C19HOP/WiSafe2-to-HomeAssistant-Bridge/HA/getting-id-from-new-device.png

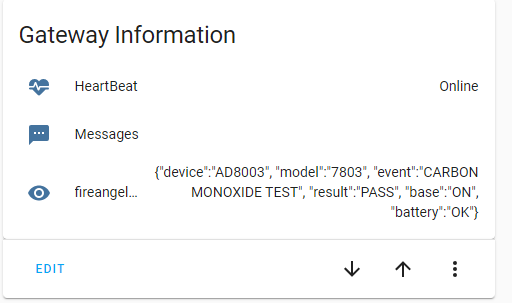
HA/getting-id-from-new-device.png
