C19HOP/WiSafe2-to-HomeAssistant-Bridge/HA/network-paired.png

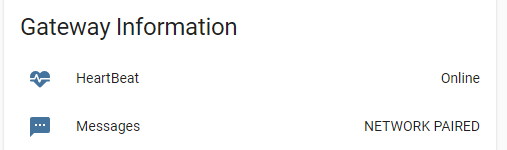
HA/network-paired.png
