C19HOP/WiSafe2-to-HomeAssistant-Bridge/WiSafeCommunicationAnalysis/PulseViewCaptures/RSWAP LOCAL 1.png

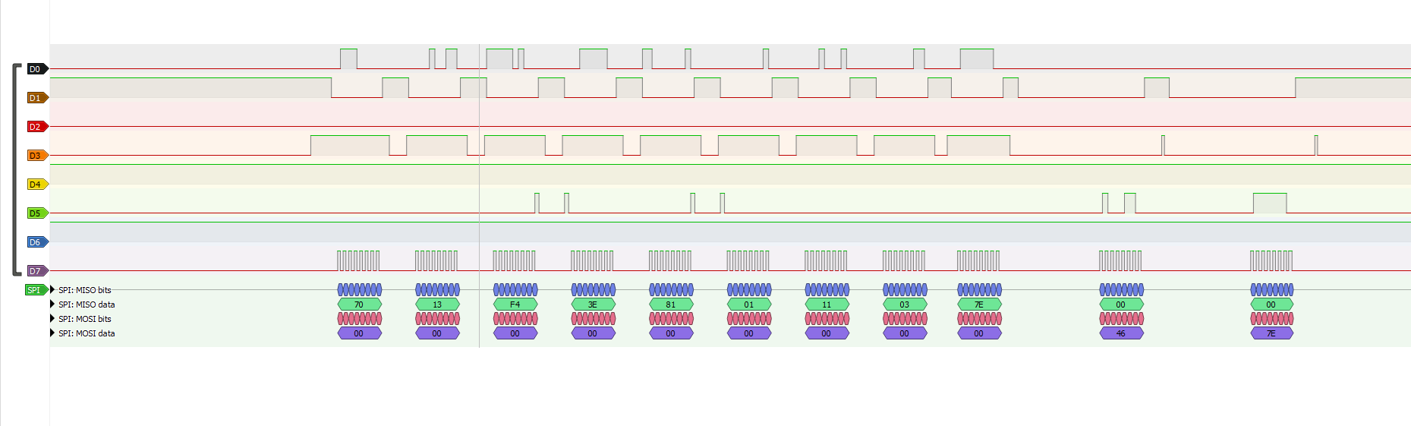
WiSafeCommunicationAnalysis/PulseViewCaptures/RSWAP LOCAL 1.png
