C19HOP/WiSafe2-to-HomeAssistant-Bridge/WiSafeCommunicationAnalysis/PulseViewCaptures/RSWAP LOCAL 2.png

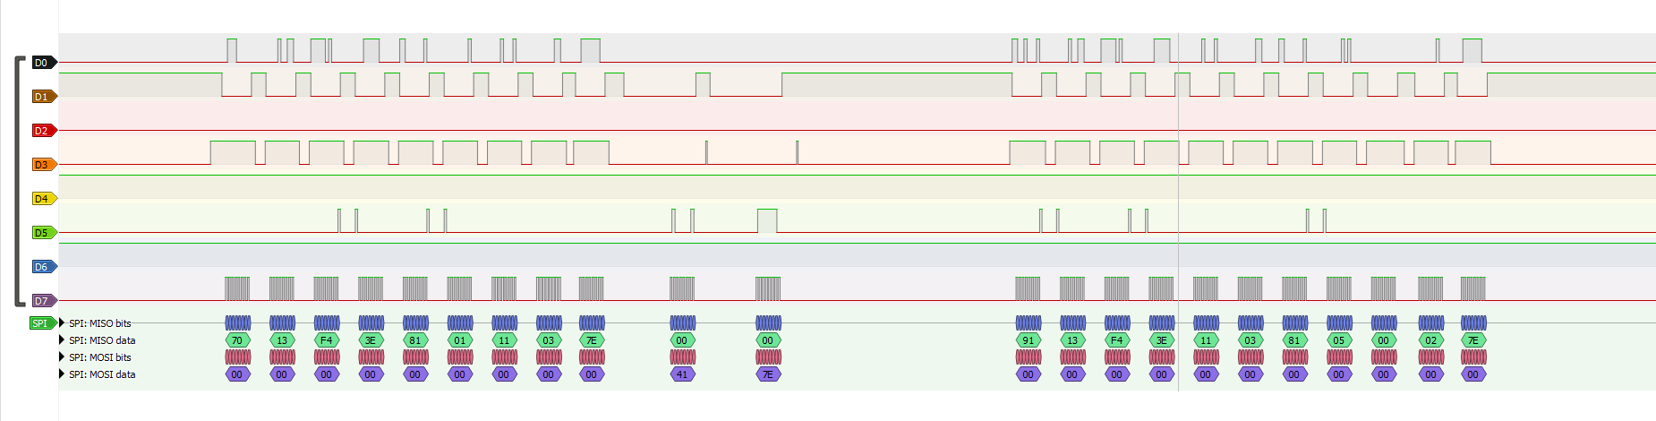
WiSafeCommunicationAnalysis/PulseViewCaptures/RSWAP LOCAL 2.png
