C19HOP/WiSafe2-to-HomeAssistant-Bridge/WiSafeCommunicationAnalysis/PulseViewCaptures/strobe/boot0.png

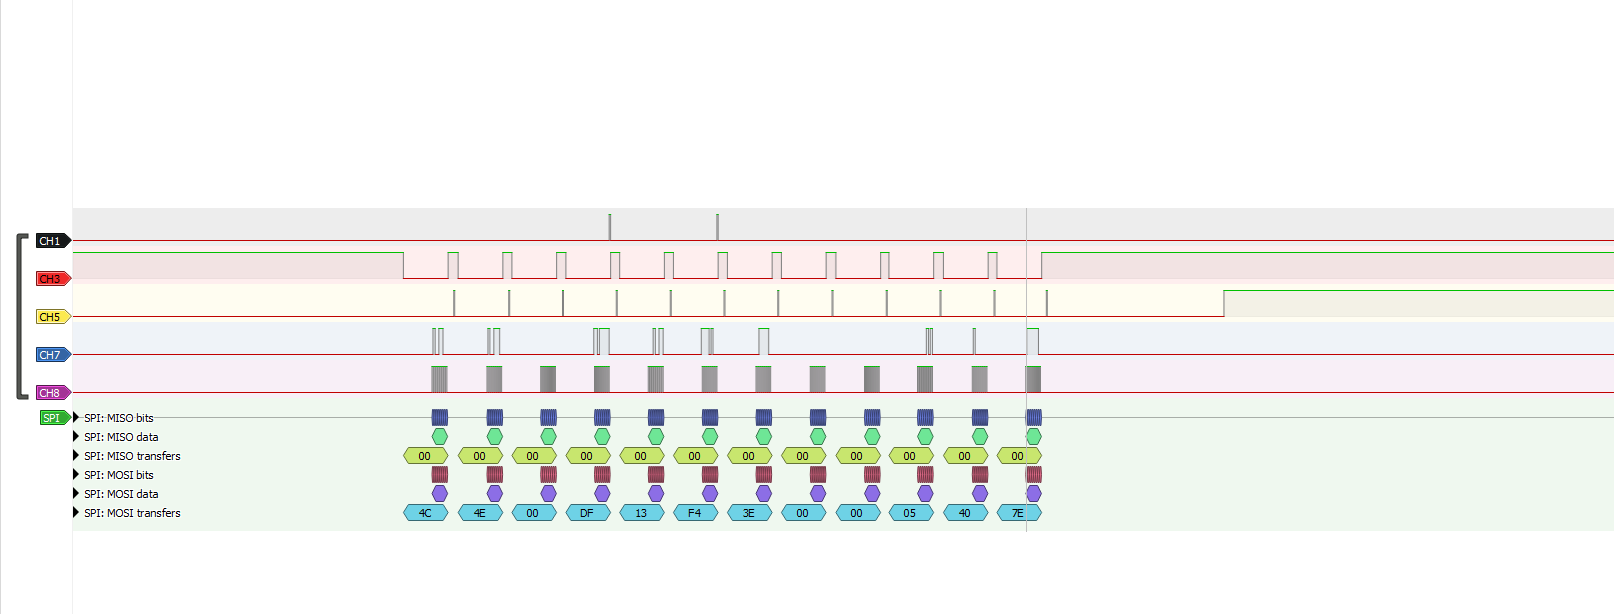
WiSafeCommunicationAnalysis/PulseViewCaptures/strobe/boot0.png
