C19HOP/WiSafe2-to-HomeAssistant-Bridge/WiSafeCommunicationAnalysis/PulseViewCaptures/strobe/boot2.png

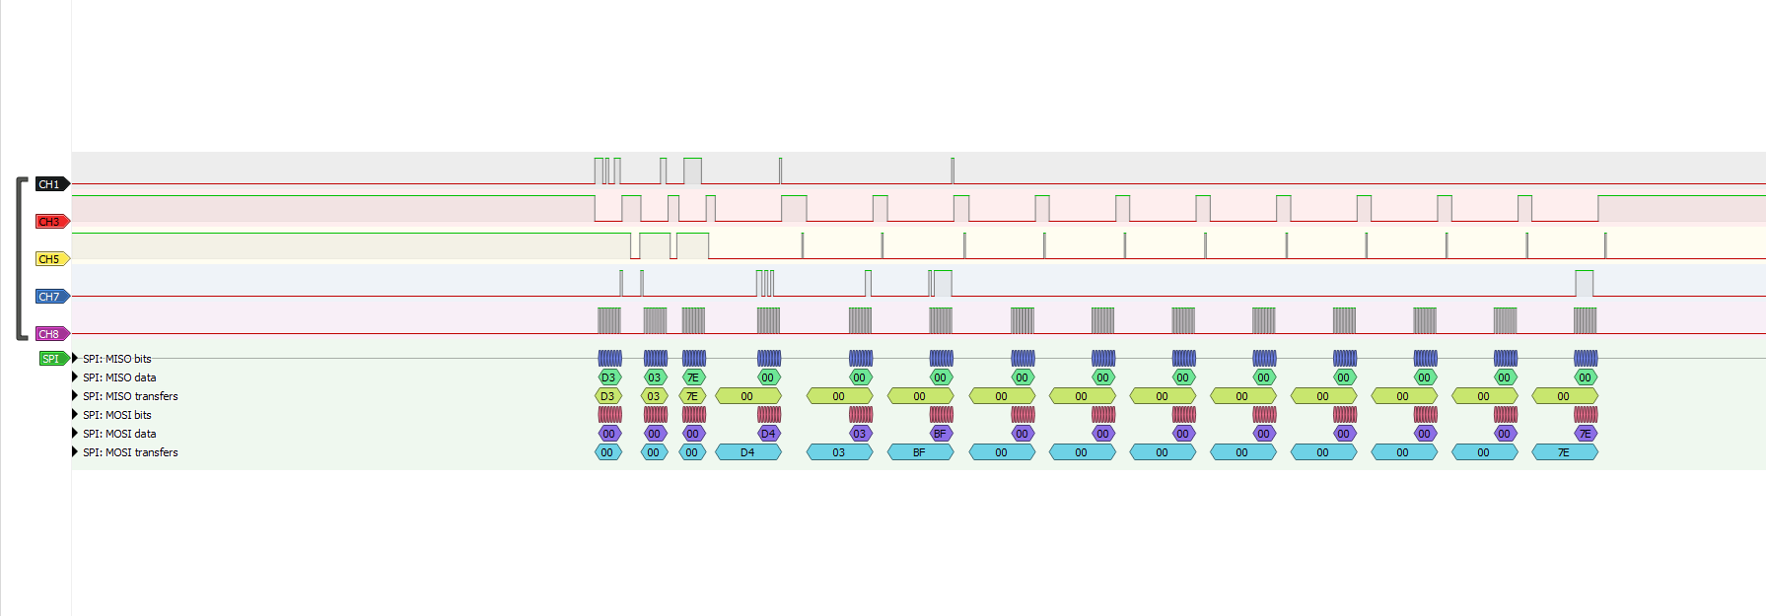
WiSafeCommunicationAnalysis/PulseViewCaptures/strobe/boot2.png
