C19HOP/WiSafe2-to-HomeAssistant-Bridge/WiSafeCommunicationAnalysis/PulseViewCaptures/strobe/boot5.png

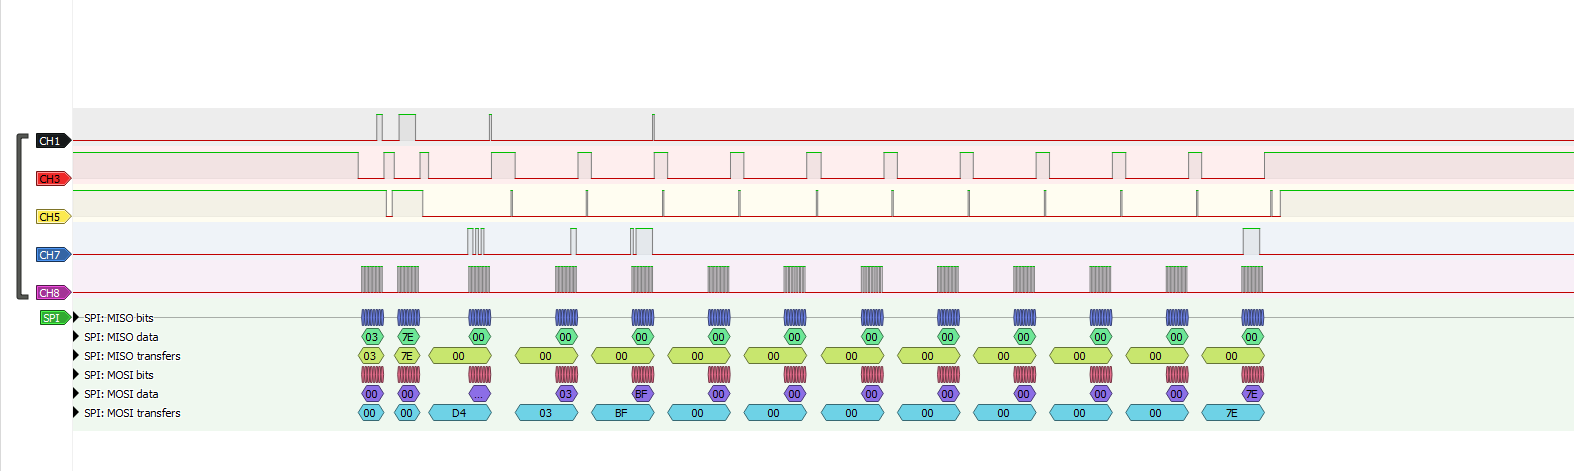
WiSafeCommunicationAnalysis/PulseViewCaptures/strobe/boot5.png
