C19HOP/WiSafe2-to-HomeAssistant-Bridge/WiSafeCommunicationAnalysis/PulseViewCaptures/strobe/boot7.png

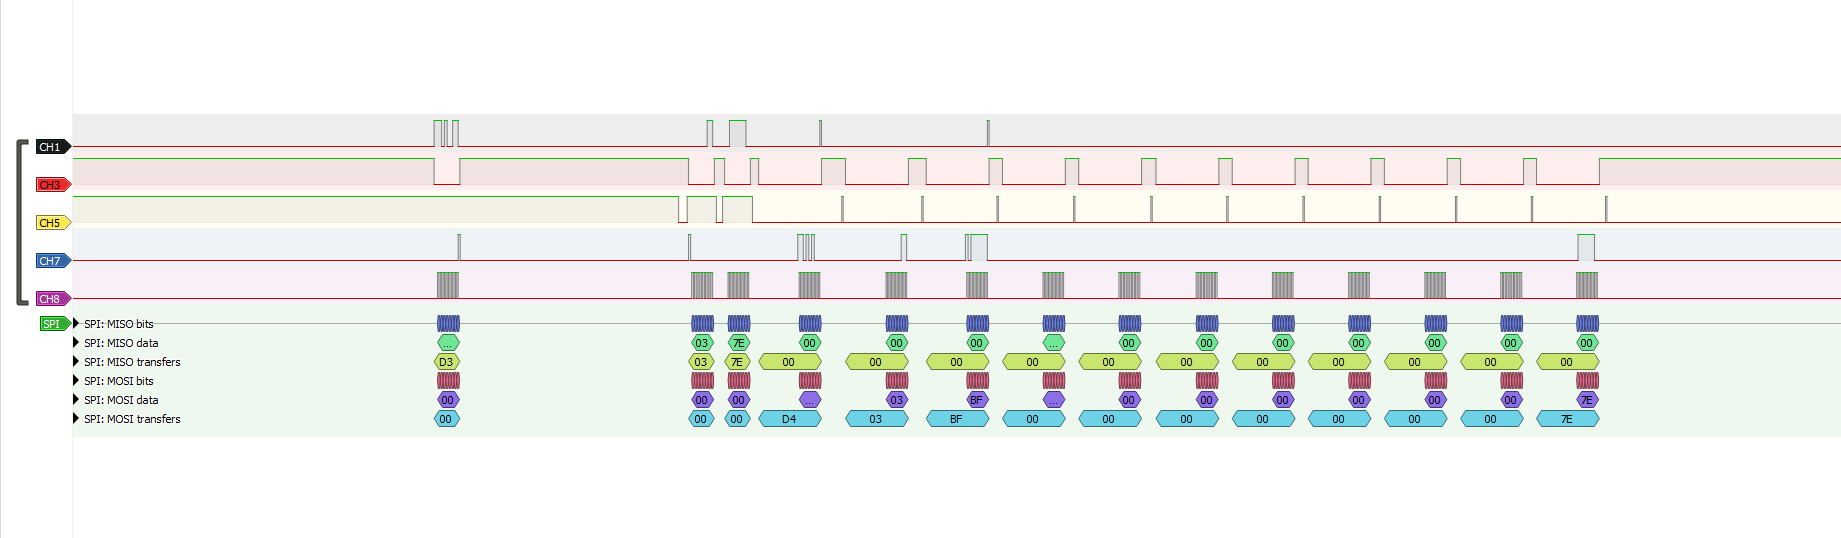
WiSafeCommunicationAnalysis/PulseViewCaptures/strobe/boot7.png
