C19HOP/WiSafe2-to-HomeAssistant-Bridge/WiSafeCommunicationAnalysis/PulseViewCaptures/strobe/new pair (from ft) part 2.png

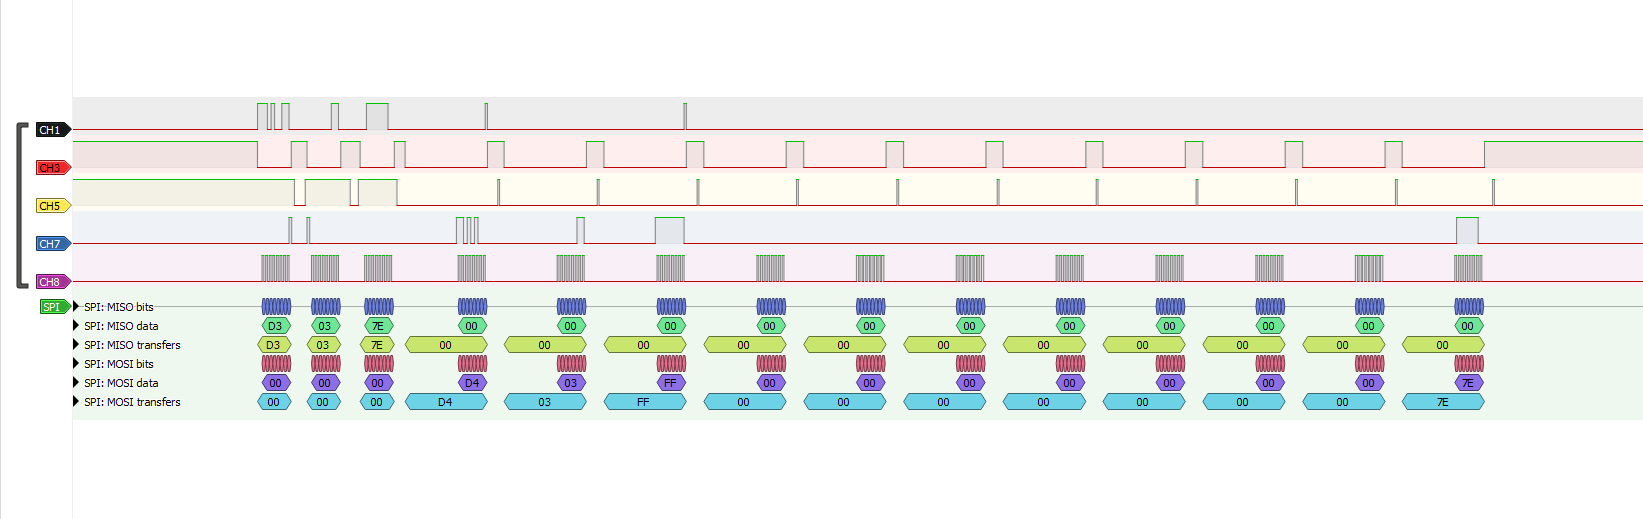
WiSafeCommunicationAnalysis/PulseViewCaptures/strobe/new pair (from ft) part 2.png
