C19HOP/WiSafe2-to-HomeAssistant-Bridge/WiSafeCommunicationAnalysis/PulseViewCaptures/strobe/radio btn 1.png

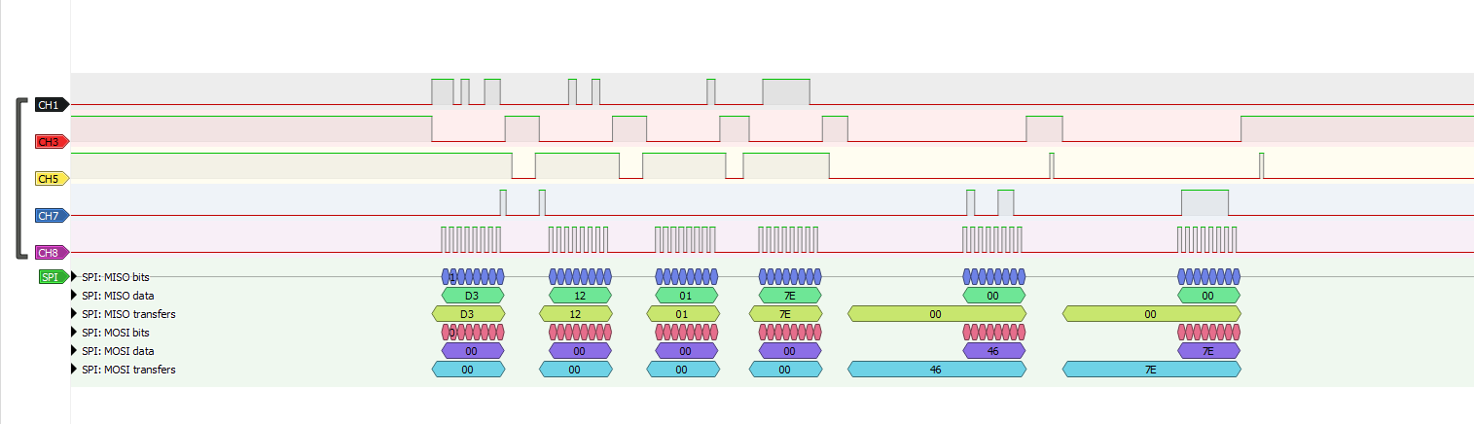
WiSafeCommunicationAnalysis/PulseViewCaptures/strobe/radio btn 1.png
