C19HOP/WiSafe2-to-HomeAssistant-Bridge/WiSafeCommunicationAnalysis/PulseViewCaptures/strobe/radio btn.png

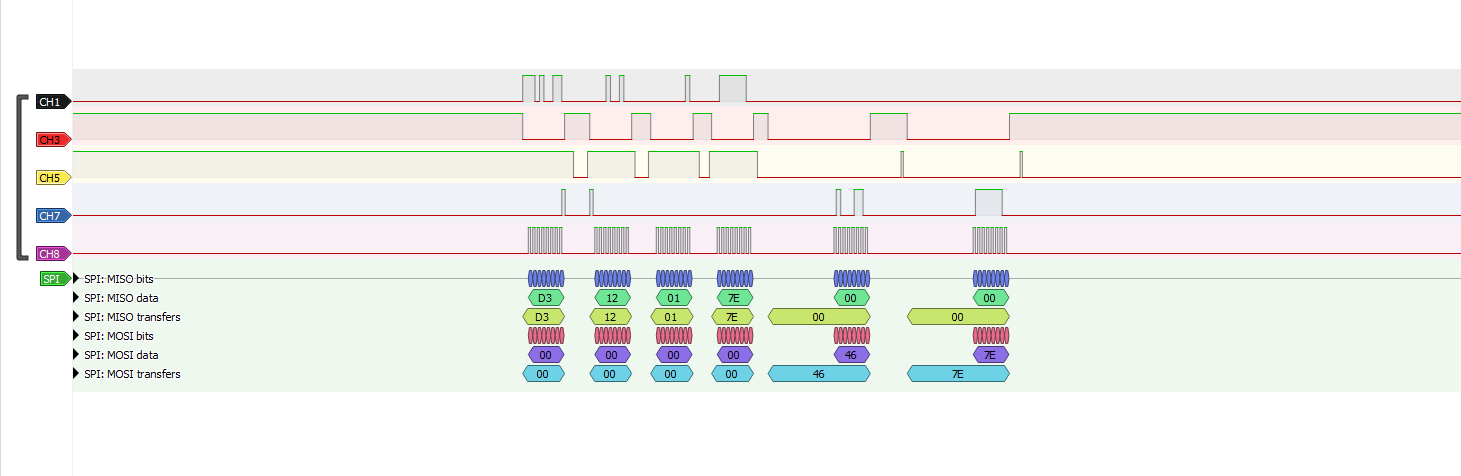
WiSafeCommunicationAnalysis/PulseViewCaptures/strobe/radio btn.png
