C19HOP/WiSafe2-to-HomeAssistant-Bridge/WiSafeCommunicationAnalysis/PulseViewCaptures/strobe/radio reset part 2.png

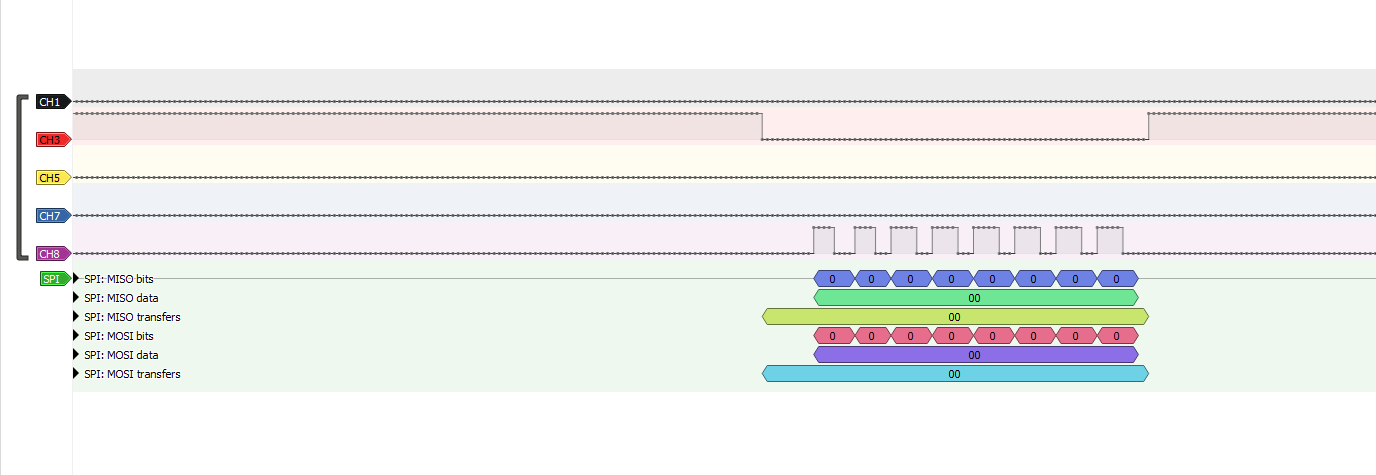
WiSafeCommunicationAnalysis/PulseViewCaptures/strobe/radio reset part 2.png
