C19HOP/WiSafe2-to-HomeAssistant-Bridge/WiSafeCommunicationAnalysis/PulseViewCaptures/strobe/rx from co 0.png

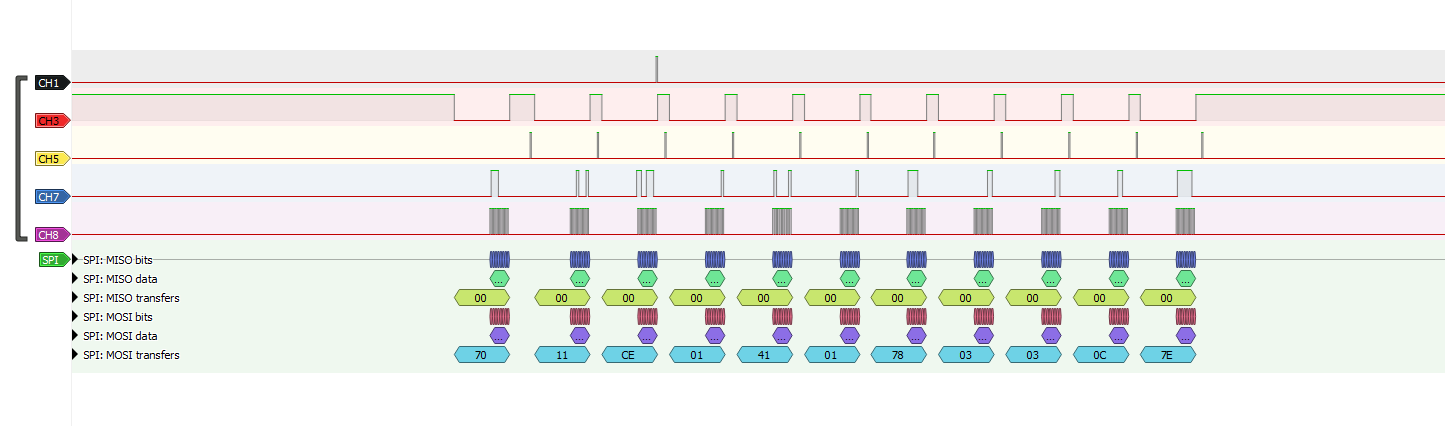
WiSafeCommunicationAnalysis/PulseViewCaptures/strobe/rx from co 0.png
