C19HOP/WiSafe2-to-HomeAssistant-Bridge/WiSafeCommunicationAnalysis/PulseViewCaptures/strobe/rx from co 1.png

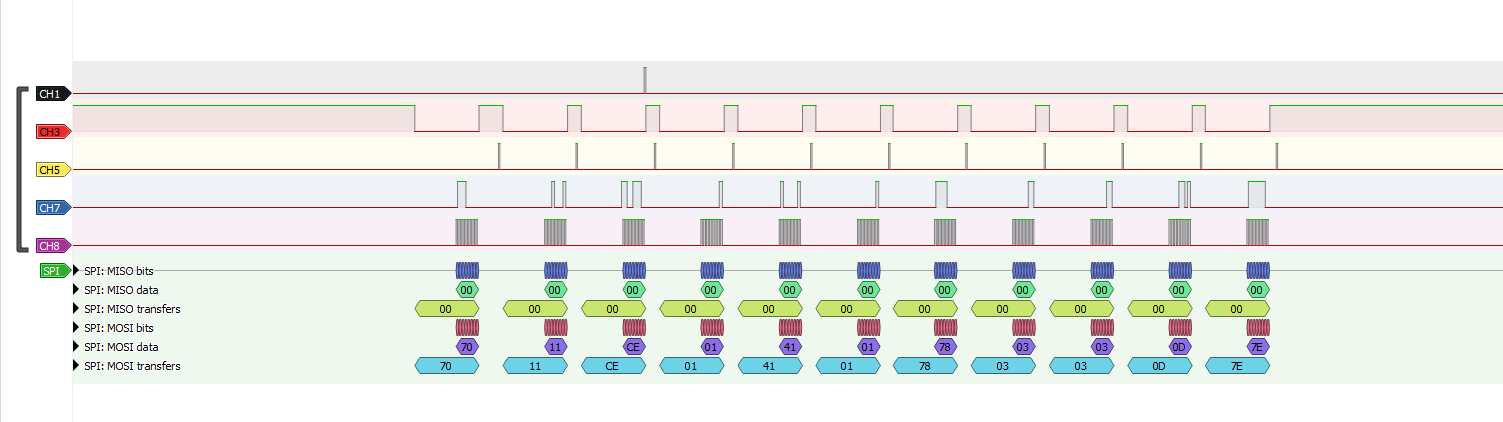
WiSafeCommunicationAnalysis/PulseViewCaptures/strobe/rx from co 1.png
