C19HOP/WiSafe2-to-HomeAssistant-Bridge/WiSafeCommunicationAnalysis/PulseViewCaptures/strobe/rx from smoke(wst630).png

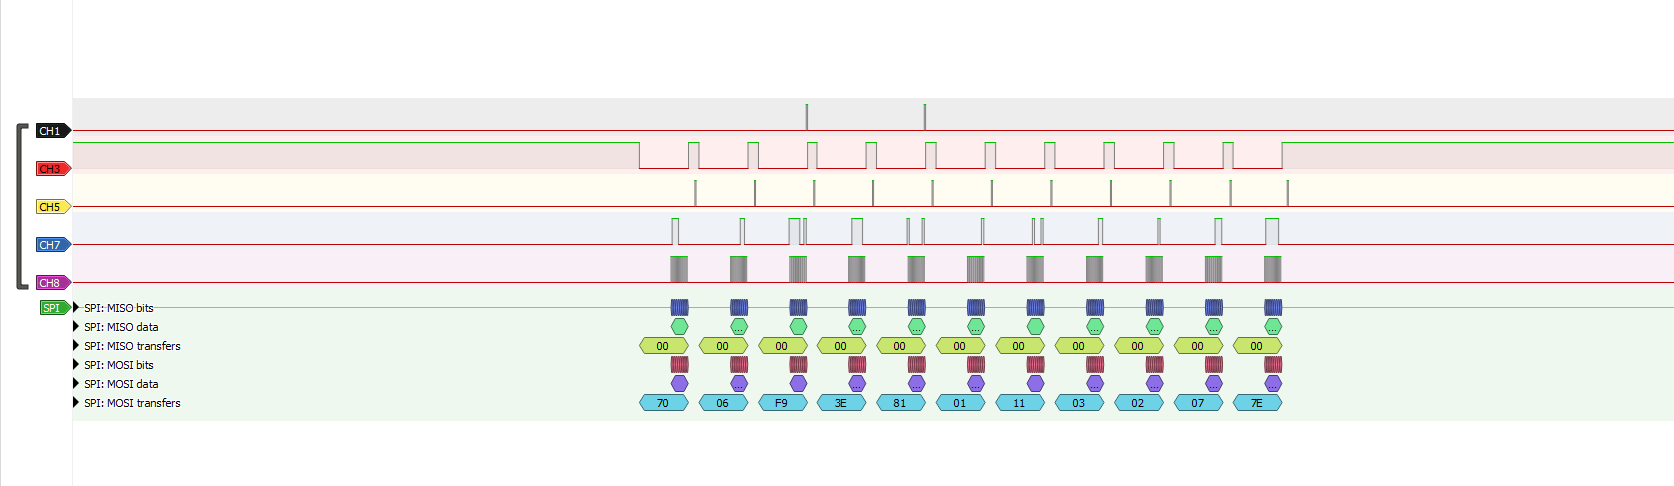
WiSafeCommunicationAnalysis/PulseViewCaptures/strobe/rx from smoke(wst630).png
