C19HOP/WiSafe2-to-HomeAssistant-Bridge/build/reverse-engineering wi-safe2 radio 3.jpg

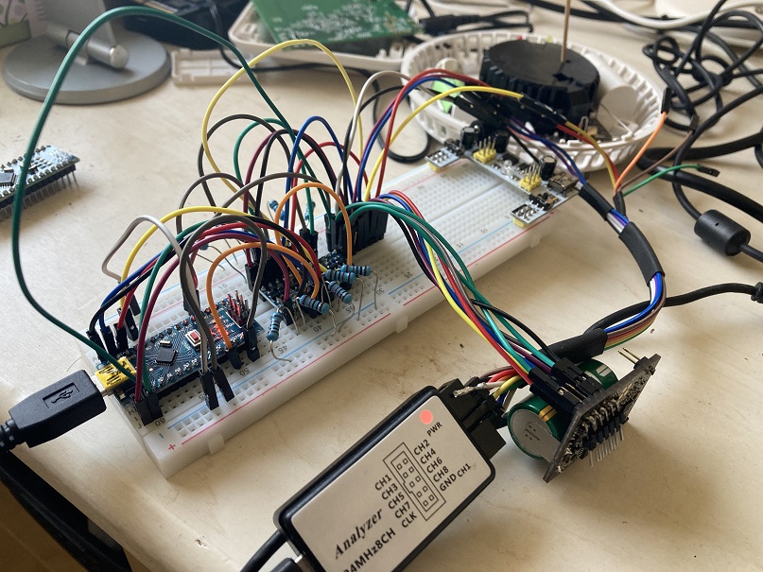
build/reverse-engineering wi-safe2 radio 3.jpg
