C19HOP/WiSafe2-to-HomeAssistant-Bridge/WiSafeCommunicationAnalysis/PulseViewCaptures/local test button 2.png

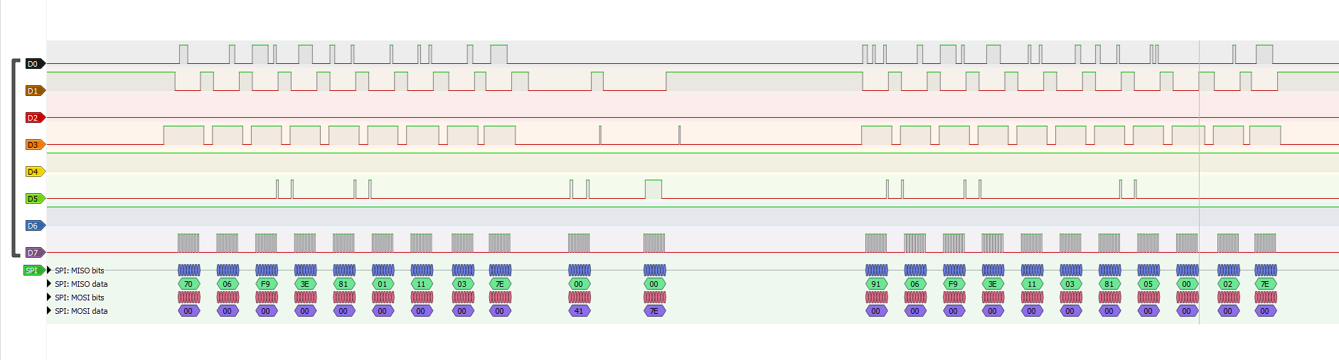
WiSafeCommunicationAnalysis/PulseViewCaptures/local test button 2.png
