C19HOP/WiSafe2-to-HomeAssistant-Bridge/WiSafeCommunicationAnalysis/PulseViewCaptures/remote test (co) TEST1.png

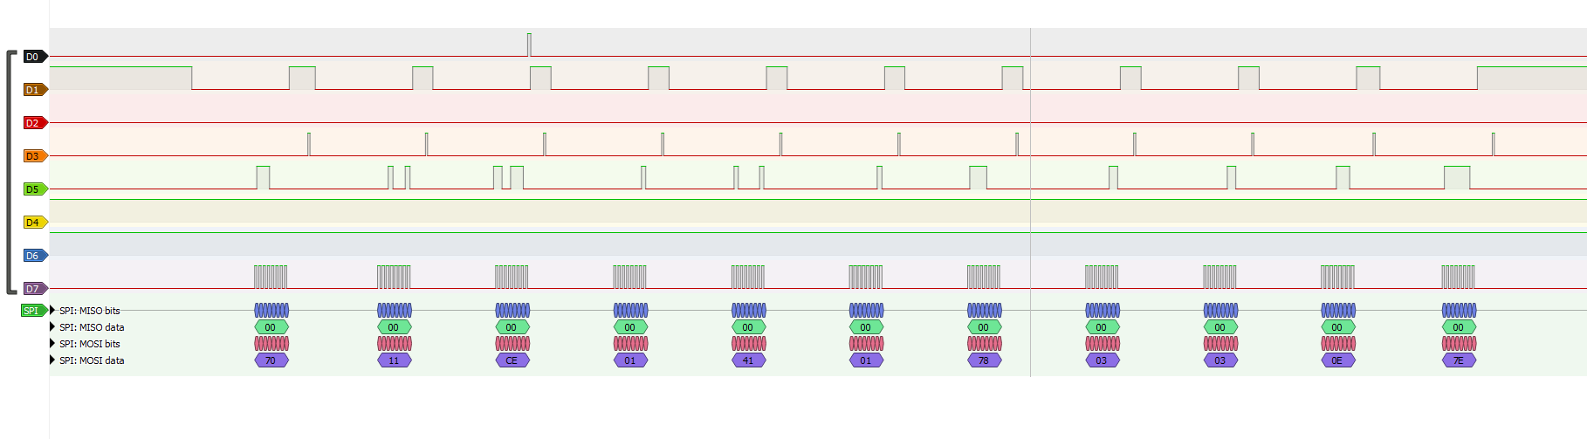
WiSafeCommunicationAnalysis/PulseViewCaptures/remote test (co) TEST1.png
