C19HOP/WiSafe2-to-HomeAssistant-Bridge/WiSafeCommunicationAnalysis/PulseViewCaptures/remote test (f) TEST3.png

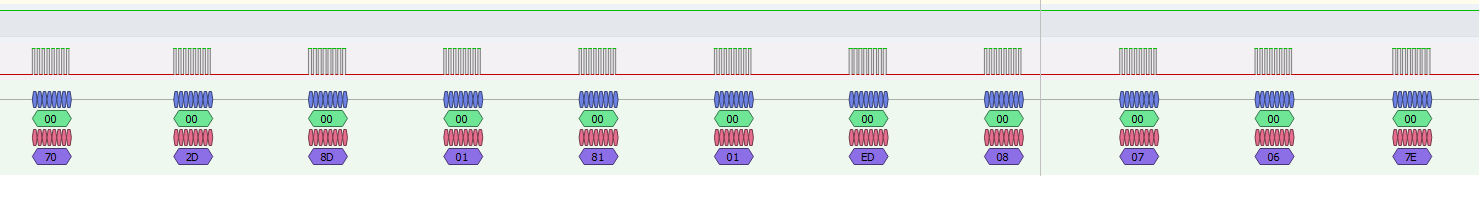
WiSafeCommunicationAnalysis/PulseViewCaptures/remote test (f) TEST3.png
