C19HOP/WiSafe2-to-HomeAssistant-Bridge/WiSafeCommunicationAnalysis/PulseViewCaptures/strobe/self-test-2.png

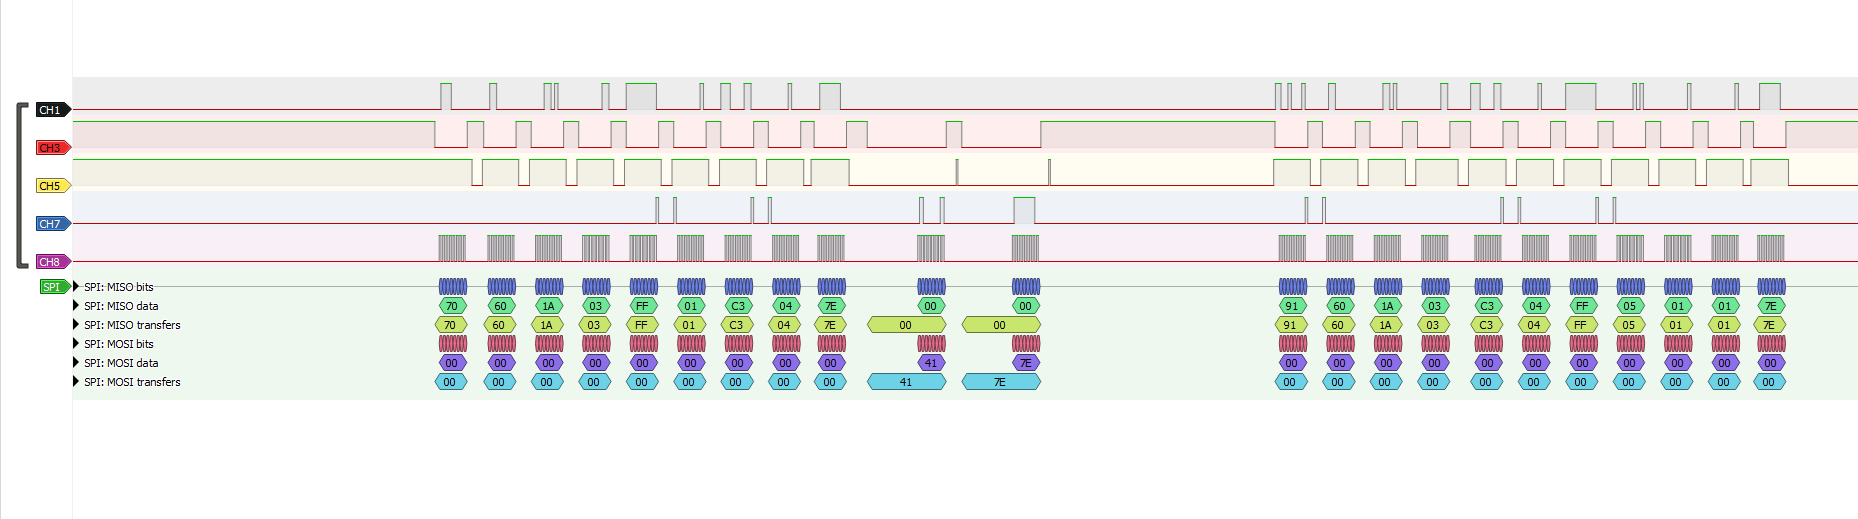
WiSafeCommunicationAnalysis/PulseViewCaptures/strobe/self-test-2.png
