C19HOP/WiSafe2-to-HomeAssistant-Bridge/WiSafeCommunicationAnalysis/PulseViewCaptures/strobe/self-test-note line 5.png

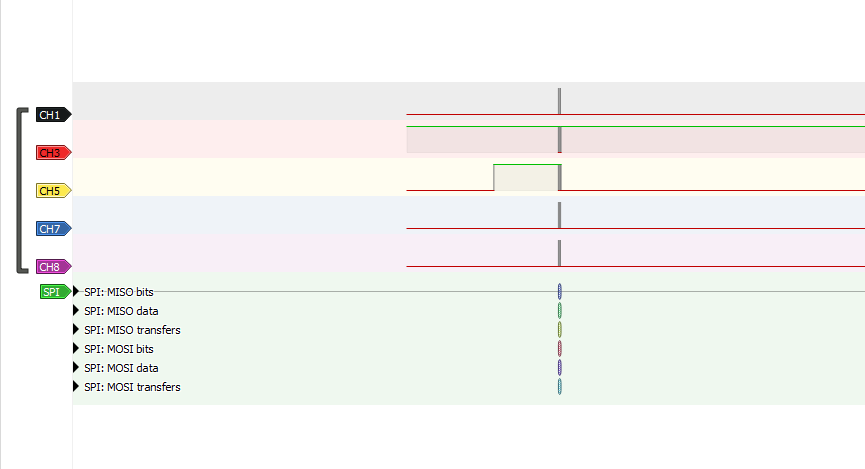
WiSafeCommunicationAnalysis/PulseViewCaptures/strobe/self-test-note line 5.png
