C19HOP/WiSafe2-to-HomeAssistant-Bridge/WiSafeCommunicationAnalysis/PulseViewCaptures/WST radio swap test1.png

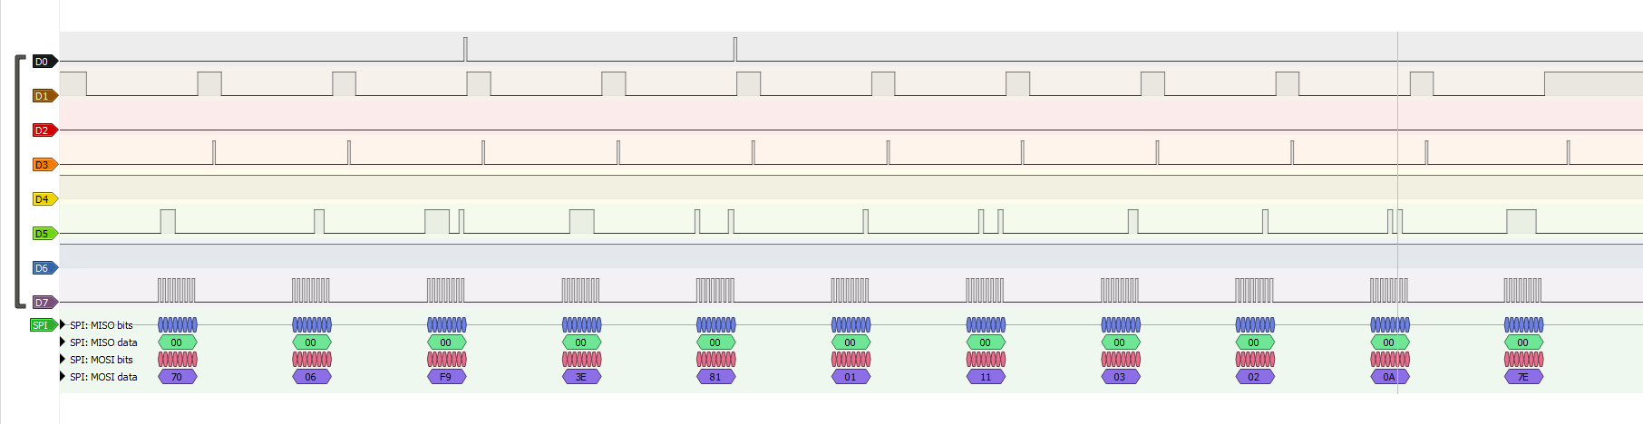
WiSafeCommunicationAnalysis/PulseViewCaptures/WST radio swap test1.png
