C19HOP/WiSafe2-to-HomeAssistant-Bridge/FireAngelProConnectedGateway/Gateway_debug_01.jpg

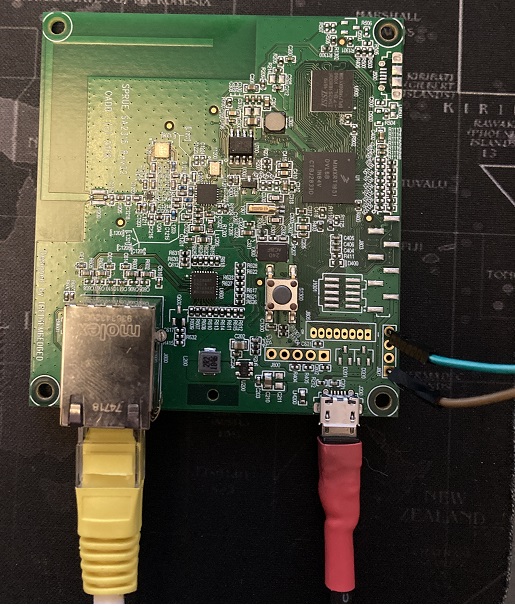
FireAngelProConnectedGateway/Gateway_debug_01.jpg
